DrJoeSweeney/DocJoesMIDIKraken/hardware/DocJoesMIDIKraken/DocJoesMIDIKraken.kicad_pcb

## KiCad design usb_blaster_ch552g/usb_blaster_ch552g.kicad_sch

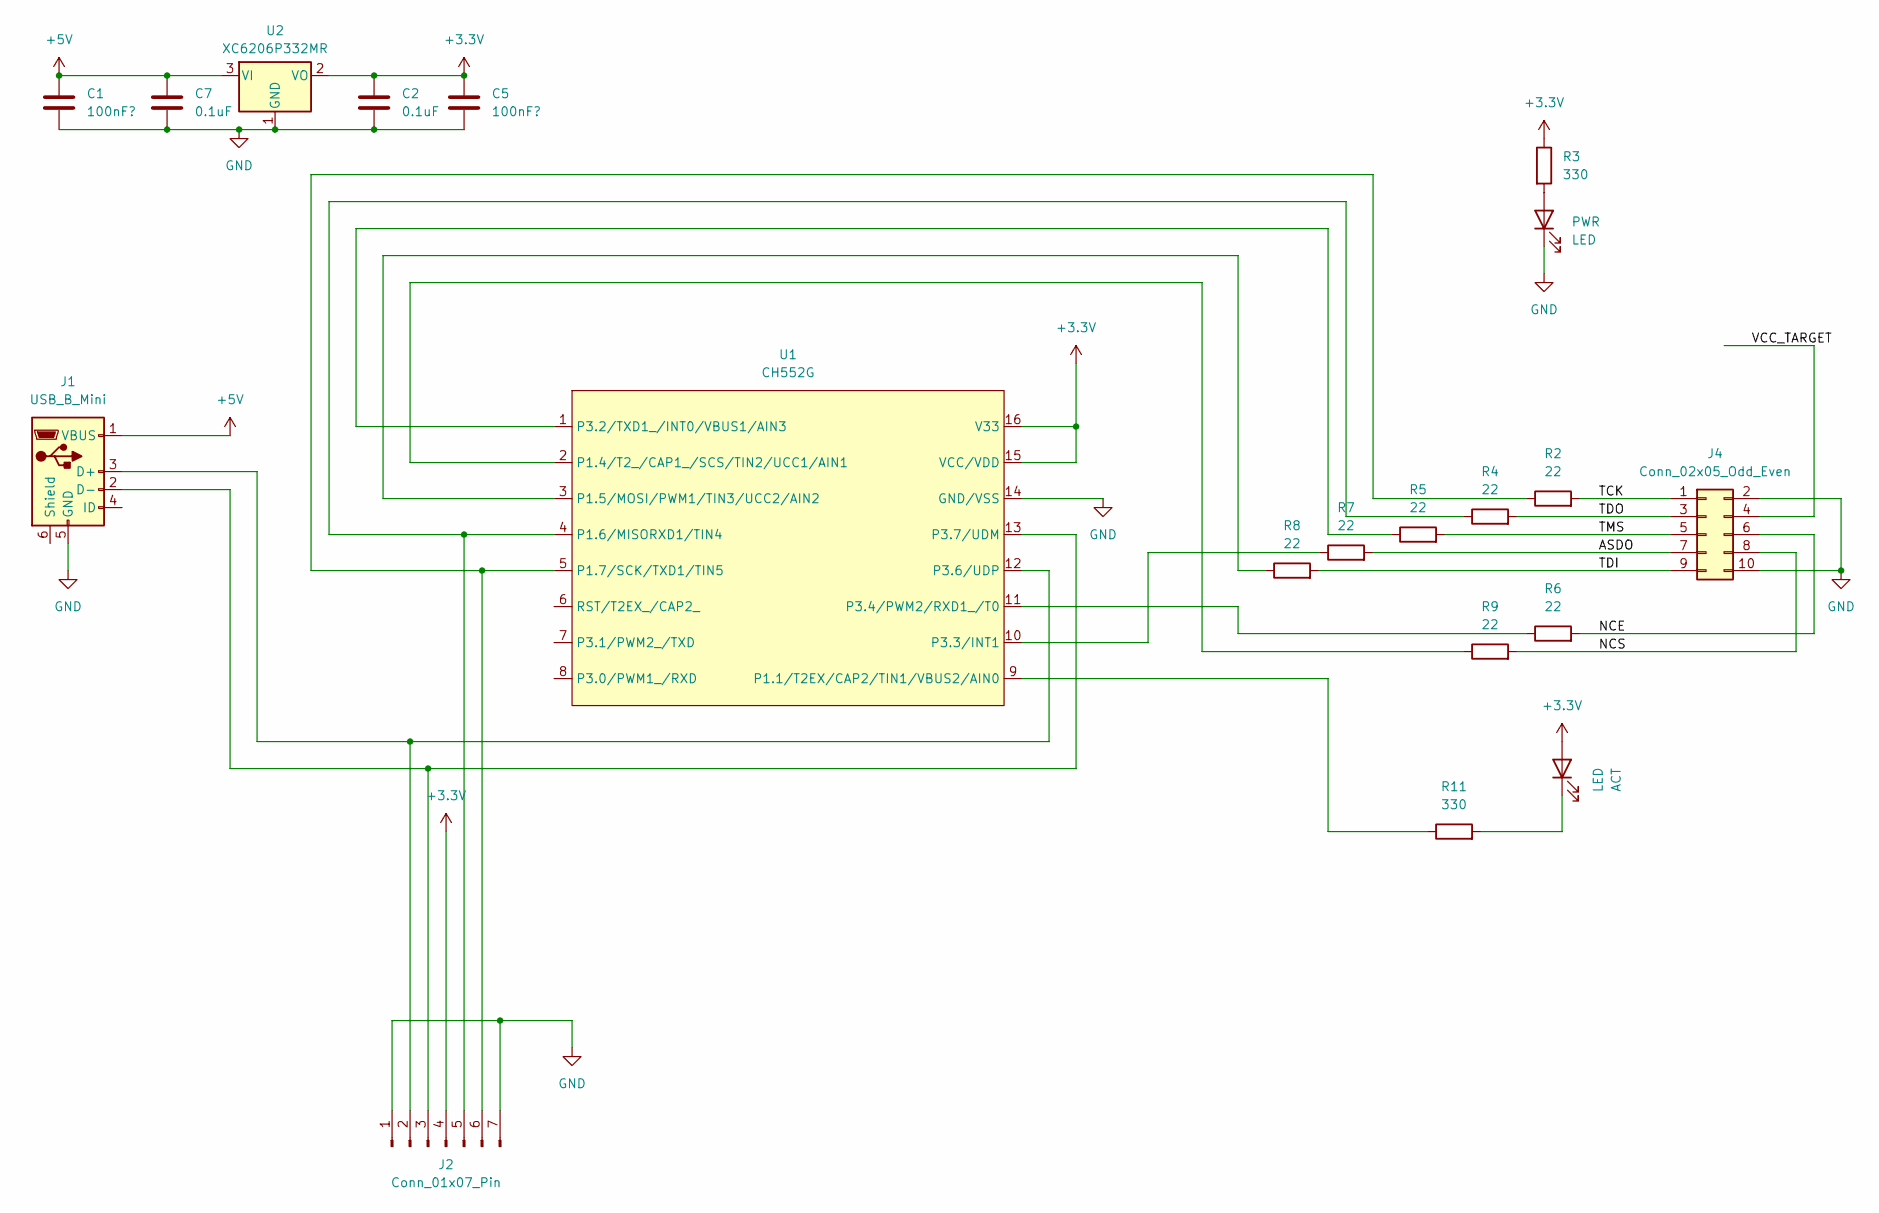
[picture p3: schematic usb_blaster_ch552g.kicad_sch]

Parts:
ACT: LED
C1, C5: 100nF?
C2, C7: 0.1uF
J1: USB_B_Mini
J2: Conn_01x07_Pin
J4: Conn_02x05_Odd_Even
PWR: LED
R2, R4, R5, R6, R7, R8, R9: 22
R3, R11: 330
U1: CH552G; SOP-16_3.9x9.9mm_P1.27mm
U2: XC6206P332MR; TO-252-3_TabPin2

Connections:
+3.3V: ACT.2 (A), C2.1, C5.1, J2.4, R3.1, U1.15 (VCC/VDD), U1.16 (V33), U2.2 (VO)
+5V: C1.1, C7.1, J1.1 (VBUS), U2.3 (VI)
ASDO: J4.7, R7.2
GND: C1.2, C2.2, C5.2, C7.2, J1.5 (GND), J2.1, J2.7, J4.2, J4.10, PWR.1 (K), U1.14 (GND/VSS), U2.1 (GND)
NCE: J4.6, R6.2
NCS: J4.8, R9.2
unnamed: ACT.1 (K), R11.2
unnamed: J1.2 (D-), J2.3, U1.13 (P3.7/UDM)
unnamed: J1.3 (D+), J2.2, U1.12 (P3.6/UDP)
unnamed: J2.5, R4.1, U1.4 (P1.6/MISORXD1/TIN4)
unnamed: J2.6, R2.1, U1.5 (P1.7/SCK/TXD1/TIN5)
unnamed: PWR.2 (A), R3.2
unnamed: R5.1, U1.1 (P3.2/TXD1_/INT0/VBUS1/AIN3)
unnamed: R6.1, U1.11 (P3.4/PWM2/RXD1_/T0)
unnamed: R7.1, U1.10 (P3.3/INT1)
unnamed: R8.1, U1.3 (P1.5/MOSI/PWM1/TIN3/UCC2/AIN2)
unnamed: R9.1, U1.2 (P1.4/T2_/CAP1_/SCS/TIN2/UCC1/AIN1)
unnamed: R11.1, U1.9 (P1.1/T2EX/CAP2/TIN1/VBUS2/AIN0)
TCK: J4.1, R2.2
TDI: J4.9, R8.2
TDO: J4.3, R4.2
TMS: J4.5, R5.2
VCC_TARGET: J4.4
